kbeckmann/ECPKart64/gateware/ecpkart64/uploader2.py

#!/usr/bin/env python3

#
# This file is part of ECPKart64.
#
# Copyright (c) 2021-2022 Konrad Beckmann <konrad.beckmann@gmail.com
# SPDX-License-Identifier: BSD-2-Clause

import os
import argparse

from tqdm import tqdm
from struct import unpack
from litex import RemoteClient
import serial

def parse_args():
    parser = argparse.ArgumentParser(description="""ECPKart64 Dump Utility""")
    parser.add_argument("--csr-csv", default="csr.csv", help="SoC CSV file")
    parser.add_argument("--file", default="bootrom.z64", help="z64 ROM file")
    parser.add_argument("--port", default="/dev/ttyUSB1", help="port")
    parser.add_argument("--baudrate", default="1000000", help="baud")
    parser.add_argument("--header", type=lambda x: int(x, 0), default=0x80371240, help="Override the first word of the ROM")
    parser.add_argument("--cic", action="store_true", help="Starts the CIC app after upload")
    args = parser.parse_args()
    return args

def main():
    args = parse_args()

    # Create and open remote control.
    if not os.path.exists(args.csr_csv):
        raise ValueError("{} not found. This is necessary to load the 'regs' of the remote. Try setting --csr-csv here to "
                         "the path to the --csr-csv argument of the SoC build.".format(args.csr_csv))

    if not os.path.exists(args.file):
        raise ValueError("{} not found.".format(args.csr_csv))

    bus = RemoteClient(csr_csv=args.csr_csv, debug=True)
    base = bus.mems.main_ram.base

    port = serial.serial_for_url(args.port, args.baudrate)

    try:
        with open(args.file, "rb") as f:
            print("Opening...")
            data_bytes = f.read()
            port.write(bytes(f"\n\n\n\nmem_load {hex(base)} {len(data_bytes)}\n".encode("utf-8")))

            chunks = (len(data_bytes) + 1023) // 1024
            with tqdm(total=chunks, desc="Uploading", bar_format="{l_bar}{bar} [ time left: {remaining} ]") as pbar:
                for chunk in range(chunks):
                    port.write(data_bytes[chunk*1024:(chunk+1)*1024])
                    pbar.update(1)

            port.write(bytes(f"set_header {hex(args.header)}\n".encode("utf-8")))
            if args.cic:
                port.write(bytes(f"cic\n".encode("utf-8")))
            f.close()
            print("Done...")

    finally:
        bus.close()

if __name__ == "__main__":
    main()
